martinhansdk/traffic_light/irsend/irsend.c

#include "irsend.h"
#include "irsendint.h"
#include "../pin_assignments.h"

#include <util/delay.h>

// Sends an IR mark for the specified number of microseconds.
// The mark output is modulated at the PWM frequency.
#define mark(time) {               \
    TIMER_ENABLE_PWM;              \
    if (time > 0) _delay_us(time); \
}

/* Leave pin off for time (given in microseconds) */
// Sends an IR space for the specified number of microseconds.
// A space is no output, so the PWM output is disabled.
#define space(time) {               \
    TIMER_DISABLE_PWM;              \
    if (time > 0) _delay_us(time);  \
}

void irsend_sendNEC(unsigned long data, int nbits)
{
  enableIROut(38);
  mark(NEC_HDR_MARK);
  space(NEC_HDR_SPACE);
  for (int i = 0; i < nbits; i++) {
    if (data & TOPBIT) {
      mark(NEC_BIT_MARK);
      space(NEC_ONE_SPACE);
    }
    else {
      mark(NEC_BIT_MARK);
      space(NEC_ZERO_SPACE);
    }
    data <<= 1;
  }
  mark(NEC_BIT_MARK);
  space(0);
}

void irsend_sendSony(unsigned long data, int nbits) {
  enableIROut(40);
  mark(SONY_HDR_MARK);
  space(SONY_HDR_SPACE);
  data = data << (32 - nbits);
  for (int i = 0; i < nbits; i++) {
    if (data & TOPBIT) {
      mark(SONY_ONE_MARK);
      space(SONY_HDR_SPACE);
    }
    else {
      mark(SONY_ZERO_MARK);
      space(SONY_HDR_SPACE);
    }
    data <<= 1;
  }
}

/*
void irsend_sendRaw(unsigned int buf[], int len, int hz)
{
  enableIROut(hz);
  for (int i = 0; i < len; i++) {
    if (i & 1) {
      space(buf[i]);
    }
    else {
      mark(buf[i]);
    }
  }
  space(0); // Just to be sure
}
*/

// Note: first bit must be a one (start bit)
void irsend_sendRC5(unsigned long data, int nbits)
{
  enableIROut(36);
  data = data << (32 - nbits);
  mark(RC5_T1); // First start bit
  space(RC5_T1); // Second start bit
  mark(RC5_T1); // Second start bit
  for (int i = 0; i < nbits; i++) {
    if (data & TOPBIT) {
      space(RC5_T1); // 1 is space, then mark
      mark(RC5_T1);
    }
    else {
      mark(RC5_T1);
      space(RC5_T1);
    }
    data <<= 1;
  }
  space(0); // Turn off at end
}


// Caller needs to take care of flipping the toggle bit
void irsend_sendRC6(unsigned long data, int nbits)
{
  enableIROut(36);
  data = data << (32 - nbits);
  mark(RC6_HDR_MARK);
  space(RC6_HDR_SPACE);
  mark(RC6_T1); // start bit
  space(RC6_T1);
  int t;
  for (int i = 0; i < nbits; i++) {
    if (i == 3) {
      // double-wide trailer bit
      t = 2;
    }
    else {
      t = 1;
    }
    if (data & TOPBIT) {
      for(int i = 0; i < t ; i++) mark(RC6_T1);
      for(int i = 0; i < t ; i++) space(RC6_T1);
    }
    else {
      for(int i = 0; i < t ; i++) space(RC6_T1);
      for(int i = 0; i < t ; i++) mark(RC6_T1);
    }

    data <<= 1;
  }
  space(0); // Turn off at end
}



void irsend_sendPanasonic(unsigned int address, unsigned long data) {
    enableIROut(35);
    mark(PANASONIC_HDR_MARK);
    space(PANASONIC_HDR_SPACE);

    for(int i=0;i<16;i++)
    {
        mark(PANASONIC_BIT_MARK);
        if (address & 0x8000) {
            space(PANASONIC_ONE_SPACE);
        } else {
            space(PANASONIC_ZERO_SPACE);
        }
        address <<= 1;
    }
    for (int i=0; i < 32; i++) {
        mark(PANASONIC_BIT_MARK);
        if (data & TOPBIT) {
            space(PANASONIC_ONE_SPACE);
        } else {
            space(PANASONIC_ZERO_SPACE);
        }
        data <<= 1;
    }
    mark(PANASONIC_BIT_MARK);
    space(0);
}
void irsend_sendJVC(unsigned long data, int nbits, int repeat)
{
    enableIROut(38);
    data = data << (32 - nbits);
    if (!repeat){
        mark(JVC_HDR_MARK);
        space(JVC_HDR_SPACE);
    }
    for (int i = 0; i < nbits; i++) {
        if (data & TOPBIT) {
            mark(JVC_BIT_MARK);
            space(JVC_ONE_SPACE);
        }
        else {
            mark(JVC_BIT_MARK);
            space(JVC_ZERO_SPACE);
        }
        data <<= 1;
    }
    mark(JVC_BIT_MARK);
    space(0);
}

void irsend_sendSAMSUNG(unsigned long data, int nbits)
{
  enableIROut(38);
  mark(SAMSUNG_HDR_MARK);
  space(SAMSUNG_HDR_SPACE);
  for (int i = 0; i < nbits; i++) {
    if (data & TOPBIT) {
      mark(SAMSUNG_BIT_MARK);
      space(SAMSUNG_ONE_SPACE);
    }
    else {
      mark(SAMSUNG_BIT_MARK);
      space(SAMSUNG_ZERO_SPACE);
    }
    data <<= 1;
  }
  mark(SAMSUNG_BIT_MARK);
  space(0);
}

void enableIROut(int khz) {
  // Enables IR output.  The khz value controls the modulation frequency in kilohertz.
  // The IR output will be on PB2
  // This routine is designed for 36-40KHz; if you use it for other values, it's up to you
  // to make sure it gives reasonable results.  (Watch out for overflow / underflow / rounding.)
  // TIMER2 is used in phase-correct PWM mode, with OCR2A controlling the frequency and OCR2B
  // controlling the duty cycle.
  // There is no prescaling, so the output frequency is 16MHz / (2 * OCR2A)
  // To turn the output on and off, we leave the PWM running, but connect and disconnect the output pin.
  // A few hours staring at the ATmega documentation and this will all make sense.
  // See my Secrets of Arduino PWM at http://arcfn.com/2009/07/secrets-of-arduino-pwm.html for details.


  // Disable the Timer1 Interrupt (which is used for receiving IR)
  TIMER_DISABLE_INTR; //Timer1 Overflow Interrupt

  // set pin to output
  set_dir_out(IR_SEND_PIN);

  // When not sending PWM, we want it low
  pin_low(IR_SEND_PIN);

  // COM2A = 00: disconnect OC2A
  // COM2B = 00: disconnect OC2B; to send signal set to 10: OC2B non-inverted
  // WGM2 = 101: phase-correct PWM with OCRA as top
  // CS2 = 000: no prescaling
  // The top value for the timer.  The modulation frequency will be SYSCLOCK / 2 / OCR2A.
  TIMER_CONFIG_KHZ(khz);
}
